74hc595/Panaplex-Clock/code/dst_dates.c

#include "dst_dates.h"
const uint16_t spring_dst_dates[16] = {
  0x0308, 0x0309, 0x0310, 0x0311, 0x0312, 0x0313, 0x0314, 0x0401, 0x0402, 0x0403, 0x0404, 0x0405, 0x0406, 0x0407, 0, 0
};

const uint16_t fall_dst_dates[16] = {
  0x1026, 0x1027, 0x1028, 0x1029, 0x1030, 0x1031, 0x1101, 0x1102, 0x1103, 0x1104, 0x1105, 0x1106, 0x1107, 0, 0, 0
};

const struct dst_date_pair dst_dates_for_year[100] = {
  {8,3}, // 2000-04-02T09:59:59.000Z -- 2000-10-29T08:59:59.000Z
  {7,2}, // 2001-04-01T09:59:59.000Z -- 2001-10-28T08:59:59.000Z
  {13,1}, // 2002-04-07T09:59:59.000Z -- 2002-10-27T08:59:59.000Z
  {12,0}, // 2003-04-06T09:59:59.000Z -- 2003-10-26T08:59:59.000Z
  {10,5}, // 2004-04-04T09:59:59.000Z -- 2004-10-31T08:59:59.000Z
  {9,4}, // 2005-04-03T09:59:59.000Z -- 2005-10-30T08:59:59.000Z
  {8,3}, // 2006-04-02T09:59:59.000Z -- 2006-10-29T08:59:59.000Z
  {3,9}, // 2007-03-11T09:59:59.000Z -- 2007-11-04T08:59:59.000Z
  {1,7}, // 2008-03-09T09:59:59.000Z -- 2008-11-02T08:59:59.000Z
  {0,6}, // 2009-03-08T09:59:59.000Z -- 2009-11-01T08:59:59.000Z
  {6,12}, // 2010-03-14T09:59:59.000Z -- 2010-11-07T08:59:59.000Z
  {5,11}, // 2011-03-13T09:59:59.000Z -- 2011-11-06T08:59:59.000Z
  {3,9}, // 2012-03-11T09:59:59.000Z -- 2012-11-04T08:59:59.000Z
  {2,8}, // 2013-03-10T09:59:59.000Z -- 2013-11-03T08:59:59.000Z
  {1,7}, // 2014-03-09T09:59:59.000Z -- 2014-11-02T08:59:59.000Z
  {0,6}, // 2015-03-08T09:59:59.000Z -- 2015-11-01T08:59:59.000Z
  {5,11}, // 2016-03-13T09:59:59.000Z -- 2016-11-06T08:59:59.000Z
  {4,10}, // 2017-03-12T09:59:59.000Z -- 2017-11-05T08:59:59.000Z
  {3,9}, // 2018-03-11T09:59:59.000Z -- 2018-11-04T08:59:59.000Z
  {2,8}, // 2019-03-10T09:59:59.000Z -- 2019-11-03T08:59:59.000Z
  {0,6}, // 2020-03-08T09:59:59.000Z -- 2020-11-01T08:59:59.000Z
  {6,12}, // 2021-03-14T09:59:59.000Z -- 2021-11-07T08:59:59.000Z
  {5,11}, // 2022-03-13T09:59:59.000Z -- 2022-11-06T08:59:59.000Z
  {4,10}, // 2023-03-12T09:59:59.000Z -- 2023-11-05T08:59:59.000Z
  {2,8}, // 2024-03-10T09:59:59.000Z -- 2024-11-03T08:59:59.000Z
  {1,7}, // 2025-03-09T09:59:59.000Z -- 2025-11-02T08:59:59.000Z
  {0,6}, // 2026-03-08T09:59:59.000Z -- 2026-11-01T08:59:59.000Z
  {6,12}, // 2027-03-14T09:59:59.000Z -- 2027-11-07T08:59:59.000Z
  {4,10}, // 2028-03-12T09:59:59.000Z -- 2028-11-05T08:59:59.000Z
  {3,9}, // 2029-03-11T09:59:59.000Z -- 2029-11-04T08:59:59.000Z
  {2,8}, // 2030-03-10T09:59:59.000Z -- 2030-11-03T08:59:59.000Z
  {1,7}, // 2031-03-09T09:59:59.000Z -- 2031-11-02T08:59:59.000Z
  {6,12}, // 2032-03-14T09:59:59.000Z -- 2032-11-07T08:59:59.000Z
  {5,11}, // 2033-03-13T09:59:59.000Z -- 2033-11-06T08:59:59.000Z
  {4,10}, // 2034-03-12T09:59:59.000Z -- 2034-11-05T08:59:59.000Z
  {3,9}, // 2035-03-11T09:59:59.000Z -- 2035-11-04T08:59:59.000Z
  {1,7}, // 2036-03-09T09:59:59.000Z -- 2036-11-02T08:59:59.000Z
  {0,6}, // 2037-03-08T09:59:59.000Z -- 2037-11-01T08:59:59.000Z
  {6,12}, // 2038-03-14T09:59:59.000Z -- 2038-11-07T08:59:59.000Z
  {5,11}, // 2039-03-13T09:59:59.000Z -- 2039-11-06T08:59:59.000Z
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
};
